jbilander/SF500/ISE/SF500/rtl/ata.v

`timescale 1ns / 1ps

module ata(
	input C14M,
	input RESET_n,
	input [23:16] A_HIGH,
	input A12,
	input A13,
	input RW_n,
	input AS_CPU_n,
	input [7:0] BASE_IDE,
	input IDE_CONFIGURED_n,
	output reg ROM_OE_n = 1'b1,
	output reg IDE_IOR_n = 1'b1,
	output reg IDE_IOW_n = 1'b1,
	output [1:0] IDE_CS_n,
	output IDE_ACCESS
);

/*
scsi.device v109.3 or oktagon.device v6.10, selectable via jumper (ROM A15-line).

scsi.device v109.3 (jumper open) is for Kickstart 2.04 and above, 
oktagon.device v6.10 (jumper closed) is for Kickstart 1.3

Keep in mind Kickstart 1.3 does not have FFS (Fast File System) in ROM, 
so in order to use FFS make a small boot-partition (e.g. ~200 MB) and format it DOS\1, 
not International (DOS\3) or DirCache (DOS\5), and not OFS (DOS\0).
https://en.wikipedia.org/wiki/Amiga_Fast_File_System
Disk's partition and filesystem information should now be stored in the RDB (Rigid Disk Block)
for autoboot to work under WB 1.3 with oktagon.device. 
To install WB 1.3: Copy all content of the WB 1.3 floppy to the formatted Drive.
*/

reg ide_enable_n = 1'b1; //Keeps track of read from ROM or IDE.

wire ide_or_rom_access = !IDE_CONFIGURED_n && (A_HIGH == BASE_IDE) && !AS_CPU_n;
assign IDE_ACCESS = !ide_enable_n && ide_or_rom_access;
assign IDE_CS_n[0] = ~A12;
assign IDE_CS_n[1] = ~A13;

/*
IDE A0-A2 are mapped on PCB like below, hence no mapping done via CPLD.
IDE_A0	<= A[9];
IDE_A1	<= A[10];
IDE_A2	<= A[11];
*/

always @(negedge RESET_n or posedge C14M) begin

	if (!RESET_n) begin
	
		IDE_IOW_n <= 1'b1;
		IDE_IOR_n <= 1'b1;
		ROM_OE_n <= 1'b1;
		ide_enable_n <= 1'b1;
		
	end else if (ide_or_rom_access) begin 
		
		if (RW_n) begin	//Read
		
			IDE_IOW_n <= 1'b1;
			IDE_IOR_n <= ide_enable_n;
			ROM_OE_n <= ~ide_enable_n;
		
		end else begin	//Write
		
			ide_enable_n <= 1'b0;
			IDE_IOW_n <= 1'b0;
			IDE_IOR_n <= 1'b1;
			ROM_OE_n <= 1'b1;
			
		end
		
	end else begin
	
		IDE_IOW_n <= 1'b1;
		IDE_IOR_n <= 1'b1;
		ROM_OE_n <= 1'b1;
		
	end

end

endmodule
